1847123212/tp78_v2/mounriver_project/BLE_CH582M/HAL/OLEDFONT.c

/********************************** (C) COPYRIGHT *******************************
 * File Name          : oledfont.c
 * Author             : ChnMasterOG
 * Version            : V1.1
 * Date               : 2022/1/26
 * Description        : OLED字体源文件
 * SPDX-License-Identifier: GPL-3.0
 *******************************************************************************
 * Attention          :
 *   常用ASCII表
 *   偏移量32
 * ASCII字符集
 *   偏移量32
 *   大小:12*6
 *   取模法：列行式(逆向 阴码)
 *******************************************************************************/

#include "HAL.h"
#include "OLEDFONT.h"

/************************************6*8的点阵************************************/
const unsigned char F6x8[][6] =		
{
0x00, 0x00, 0x00, 0x00, 0x00, 0x00,// sp - empty
0x00, 0x00, 0x00, 0x2f, 0x00, 0x00,// !
0x00, 0x00, 0x07, 0x00, 0x07, 0x00,// "
0x00, 0x14, 0x7f, 0x14, 0x7f, 0x14,// #
0x00, 0x24, 0x2a, 0x7f, 0x2a, 0x12,// $
0x00, 0x62, 0x64, 0x08, 0x13, 0x23,// %
0x00, 0x36, 0x49, 0x55, 0x22, 0x50,// &
0x00, 0x00, 0x05, 0x03, 0x00, 0x00,// '
0x00, 0x00, 0x1c, 0x22, 0x41, 0x00,// (
0x00, 0x00, 0x41, 0x22, 0x1c, 0x00,// )
0x00, 0x14, 0x08, 0x3E, 0x08, 0x14,// *
0x00, 0x08, 0x08, 0x3E, 0x08, 0x08,// +
0x00, 0x00, 0x00, 0xA0, 0x60, 0x00,// ,
0x00, 0x08, 0x08, 0x08, 0x08, 0x08,// -
0x00, 0x00, 0x60, 0x60, 0x00, 0x00,// .
0x00, 0x20, 0x10, 0x08, 0x04, 0x02,// /
0x00, 0x3E, 0x51, 0x49, 0x45, 0x3E,// 0
0x00, 0x00, 0x42, 0x7F, 0x40, 0x00,// 1
0x00, 0x42, 0x61, 0x51, 0x49, 0x46,// 2
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
  0xE4,0xC4,0xC8,0x88,0x10,0x20,0xC0,0x00,0x00,0x00,0x00,0x00,0x00,0x00,0x00,0x00,
  0x00,0x00,0x00,0x80,0xE0,0xE0,0xE4,0x84,0x04,0x08,0x08,0x10,0x20,0xC0,0x00,0x00,
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
};

/*********************************************END OF FILE**********************/
